masa-0021/bmw-seat/doc/schematics/schematics.kicad_sch

## KiCad design doc/schematics/schematics.kicad_sch (2026-03-22)

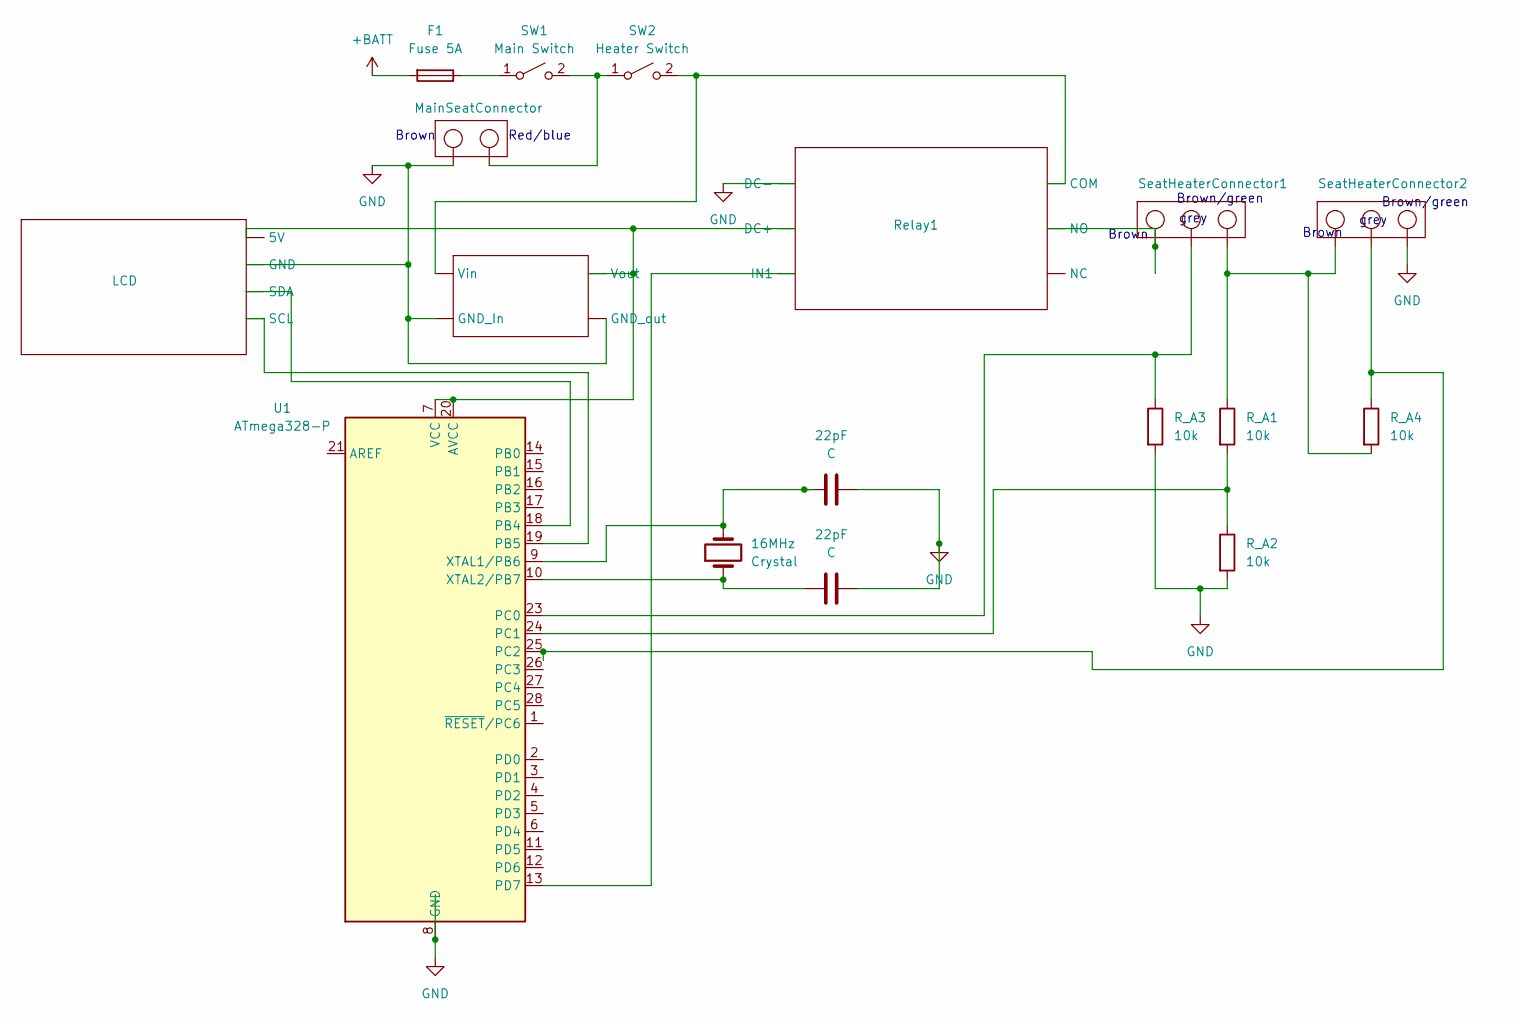
[picture p4: schematic schematics.kicad_sch]

Parts:
16MHz: Crystal
22pF: C
F1: Fuse 5A
LCD: (no value)
MainSeatConnector: (no value)
R_A1, R_A2, R_A3, R_A4: 10k
Relay1: (no value)
SW1: Main Switch
SW2: Heater Switch
SeatHeaterConnector1, SeatHeaterConnector2: (no value)
U1: ATmega328-P; DIP-28_W7.62mm
U3: (no value)

Connections:
+BATT: F1.2
GND: 22pF.2, LCD., MainSeatConnector., R_A2.2, R_A3.2, Relay1., SeatHeaterConnector2., U1.8 (GND), U1.22 (GND), U3.
unnamed: 16MHz.1, 22pF.1, U1.10 (XTAL2/PB7)
unnamed: 16MHz.2, 22pF.1, U1.9 (XTAL1/PB6)
unnamed: F1.1, SW1.1 (A)
unnamed: LCD., Relay1., U1.7 (VCC), U1.18 (PB4), U1.19 (PB5), U1.20 (AVCC), U3.
unnamed: MainSeatConnector., SW1.2 (B), SW2.1 (A)
unnamed: R_A1.1, R_A4.2, SeatHeaterConnector1., SeatHeaterConnector2.
unnamed: R_A1.2, R_A2.1, U1.24 (PC1)
unnamed: R_A3.1, SeatHeaterConnector1., U1.23 (PC0)
unnamed: R_A4.1, SeatHeaterConnector2., U1.25 (PC2)
unnamed: Relay1., SW2.2 (B), SeatHeaterConnector1., U1.13 (PD7), U3.

Notes on the sheet:
Brown/green
Brown
grey
Red/blue
